OpenLightingProject/rp2040-dmxsun/src/tusb_lwip_glue.c

/* 
 * The MIT License (MIT)
 *
 * Based on tinyUSB example that is: Copyright (c) 2020 Peter Lawrence
 * Modified for Pico by Floris Bos
 *
 * influenced by lrndis https://github.com/fetisov/lrndis
 *
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
 */

#include "tusb_lwip_glue.h"
#include <pico/unique_id.h>

#include "log.h"

#include "boardconfig.h"
#include "dhcpdata.h"

extern uint8_t usbTraffic;

/* lwip context */
static struct netif netif_data;

/* shared between tud_network_recv_cb() and service_traffic() */
static struct pbuf *received_frame;

/* this is used by this code, ./class/net/net_driver.c, and usb_descriptors.c */
/* ideally speaking, this should be generated from the hardware's unique ID (if available) */
/* it is suggested that the first byte is 0x02 to indicate a link-local address */
uint8_t tud_network_mac_address[6] = {0x02,0x02,0x84,0x6A,0x96,0x00};

ip_addr_t ipaddr;
ip_addr_t netmask;
ip_addr_t gateway;

ip_addr_t hostIp;
ip_addr_t ownIp;

static err_t linkoutput_fn(struct netif *netif, struct pbuf *p)
{
    (void)netif;

    for (;;)
    {
        /* if TinyUSB isn't ready, we must signal back to lwip that there is nothing we can do */
        if (!tud_ready()) {
            return ERR_USE;
        }

        /* if the network driver can accept another packet, we make it happen */
        if (tud_network_can_xmit(p->tot_len))
        {
          tud_network_xmit(p, 0 /* unused for this example */);
          return ERR_OK;
        }
    
      /* transfer execution to TinyUSB in the hopes that it will finish transmitting the prior packet */
      tud_task();
     }
}

static err_t output_fn(struct netif *netif, struct pbuf *p, const ip_addr_t *addr)
{
    return etharp_output(netif, p, addr);
}

static void netif_status_callback(struct netif *nif)
{
  LOG("netif_status_callback: %c%c%d is %s\n", nif->name[0], nif->name[1], nif->num, netif_is_up(nif) ? "UP" : "DOWN");
}

static void netif_link_callback(struct netif *state_netif)
{
  if (netif_is_link_up(state_netif)) {
    LOG("netif_link_callback==UP\n");
  } else {
    LOG("netif_link_callback==DOWN\n");
  }
}

static err_t netif_init_cb(struct netif *netif)
{
    LOG("netif_init_cb");
    LWIP_ASSERT("netif != NULL", (netif != NULL));
    netif->mtu = CFG_TUD_NET_MTU;
    netif->flags = NETIF_FLAG_BROADCAST | NETIF_FLAG_ETHARP | NETIF_FLAG_LINK_UP | NETIF_FLAG_UP;
    netif->state = NULL;
    netif->name[0] = 'u'; // for "USB"
    netif->name[1] = '0';
    netif->linkoutput = linkoutput_fn;
    netif->output = output_fn;

    netif->hostname = getBoardHostnameString();

    return ERR_OK;
}

void init_tinyusb_netif(void)
{
    struct netif *netif = &netif_data;
    err_t igmp_result;
    
    /* Fixup MAC address based on flash serial */
    pico_unique_board_id_t id;
    pico_get_unique_board_id(&id);
    
    /* the lwip virtual MAC address must be different from the host's; to ensure this, we toggle the LSbit */
    netif->hwaddr_len = sizeof(tud_network_mac_address);
    memcpy(netif->hwaddr+1, (id.id)+1, sizeof(tud_network_mac_address)-1);
    netif->hwaddr[0] = 0x02;
    netif->hwaddr[5] ^= 0x01;

    ip4_addr_set_u32(&ipaddr, getOwnIp());
    ip4_addr_set_u32(&netmask, getOwnMask());
    ip4_addr_set_u32(&gateway, 0);
    
    netif = netif_add(netif, &ipaddr, &netmask, &gateway, NULL, netif_init_cb, ip_input);
    netif_set_status_callback(netif, netif_status_callback);
    netif_set_link_callback(netif, netif_link_callback);
    netif_set_default(netif);


    netif->flags |= NETIF_FLAG_IGMP;
    igmp_result = igmp_start( netif );
    LOG("IGMP START: %u", igmp_result);
}

void tud_network_init_cb(void)
{
    /* if the network is re-initializing and we have a leftover packet, we must do a cleanup */
    if (received_frame)
    {
      pbuf_free(received_frame);
      received_frame = NULL;
    }
}

bool tud_network_recv_cb(const uint8_t *src, uint16_t size)
{
    /* this shouldn't happen, but if we get another packet before 
    parsing the previous, we must signal our inability to accept it */
    if (received_frame) return false;

    usbTraffic = 1;
    
    if (size)
    {
        struct pbuf *p = pbuf_alloc(PBUF_RAW, size, PBUF_POOL);

        if (p)
        {
            /* pbuf_alloc() has already initialized struct; all we need to do is copy the data */
            memcpy(p->payload, src, size);
        
            /* store away the pointer for service_traffic() to later handle */
            received_frame = p;
        }
    }

    return true;
}

uint16_t tud_network_xmit_cb(uint8_t *dst, void *ref, uint16_t arg)
{
    struct pbuf *p = (struct pbuf *)ref;

    (void)arg; /* unused for this example */

    pbuf_copy_partial(p, dst, p->tot_len, 0);

    return p->tot_len;
}

void service_traffic(void)
{
    /* handle any packet received by tud_network_recv_cb() */
    if (received_frame)
    {
      ethernet_input(received_frame, &netif_data);
      pbuf_free(received_frame);
      received_frame = NULL;
      tud_network_recv_renew();
    }
    
    sys_check_timeouts();
}

// Should moved out of here, at least the "start DHCP server" part
void dhcpd_init()
{
    ip4_addr_set_u32(&hostIp, getHostIp());
    dhcp_entries_usb[0].addr = hostIp;
    dhcp_entries_usb[0].lease = 24 * 60 * 60;

    dhcp_config_usb->netif = &netif_data;

    while (dhserv_init(&dhcp_config) != ERR_OK);
}

void wait_for_netif_is_up()
{
    LOG("wait_for_netif_is_up: %u", netif_is_up(&netif_data));
    while (!netif_is_up(&netif_data));
}


/* lwip platform specific routines for Pico */
auto_init_mutex(lwip_mutex);
static int lwip_mutex_count = 0;
