OpenLightingProject/rp2040-dmxsun/src/lwipopts.h

/*
 * Copyright (c) 2001-2003 Swedish Institute of Computer Science.
 * All rights reserved. 
 * 
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
 * This file is part of the lwIP TCP/IP stack.
 * 
 * Author: Simon Goldschmidt
 *
 */
#ifndef __LWIPOPTS_H__
#define __LWIPOPTS_H__

/* Prevent having to link sys_arch.c (we don't test the API layers in unit tests) */
#define NO_SYS                          1
#define MEM_ALIGNMENT                   4
#define MEM_SIZE                        16384  // default: 1600
#define PBUF_POOL_SIZE                  24     // default: 16
#define MEMP_NUM_UDP_PCB                64
#define MEMP_NUM_TCP_PCB                16
#define MEMP_NUM_TCPIP_MSG_API          16
#define LWIP_RAW                        0
#define LWIP_NETCONN                    0
#define LWIP_SOCKET                     0
#define LWIP_DHCP                       1
#define LWIP_DNS                        1
#define LWIP_NETIF_HOSTNAME             1
#define LWIP_ICMP                       1
#define LWIP_UDP                        1
#define LWIP_TCP                        1
#define LWIP_SNMP                       0
#define LWIP_PPP                        0
#define LWIP_IPV6                       0
#define ETH_PAD_SIZE                    0
#define LWIP_IP_ACCEPT_UDP_PORT(p)      ((p) == PP_NTOHS(67))

#define LWIP_IGMP                       1
#define MEMP_NUM_IGMP_GROUP             32

#define TCP_MSS                         (1500 /*mtu*/ - 20 /*iphdr*/ - 20 /*tcphhr*/)
#define TCP_SND_BUF                     (2 * TCP_MSS)

#define ETHARP_SUPPORT_STATIC_ENTRIES   1

#define LWIP_NETIF_STATUS_CALLBACK      1
#define LWIP_NETIF_LINK_CALLBACK        1

#define LWIP_HTTPD_CGI                  1
#define LWIP_HTTPD_SSI                  1
#define LWIP_HTTPD_SSI_RAW              1
#define LWIP_HTTPD_MAX_TAG_NAME_LEN     64
#define LWIP_HTTPD_SSI_INCLUDE_TAG      0
#define LWIP_HTTPD_MAX_TAG_INSERT_LEN   2048

#define LWIP_HTTPD_SUPPORT_11_KEEPALIVE 1

#define HTTPD_USE_CUSTOM_FSDATA         1
#define HTTPD_FSDATA_FILE               "../../../../../src/fsdata.c"

#define LWIP_SINGLE_NETIF               0

// Defined in https://github.com/raspberrypi/pico-examples/blob/master/pico_w/lwipopts_examples_common.h
#define LWIP_NETIF_TX_SINGLE_PBUF   1
#define MEM_LIBC_MALLOC             1

#endif /* __LWIPOPTS_H__ */
