OpenLightingProject/rp2040-dmxsun/src/dmxbuffer.h

#ifndef DMXBUFFER_H
#define DMXBUFFER_H

#include <cstdint>
#include <stdio.h>

#ifndef DMXBUFFER_COUNT
#define DMXBUFFER_COUNT 24
#endif // DMXBUFFER_COUNT

#ifdef __cplusplus

// Class that stores and manages ALL internal "main" DMX buffers
class DmxBuffer {
  public:
    static uint8_t buffer[DMXBUFFER_COUNT][512];
    static uint8_t allZeroes[512]; // Array of 512 zero-bytes to be used with memcmp for performance
    void init();
    void zero(uint8_t bufferId);
    bool getBuffer(uint8_t bufferId, uint8_t* dest, uint16_t destLength); // alias "copyTo"
    bool setBuffer(uint8_t bufferId, uint8_t* source, uint16_t sourceLength); // alias "copyFrom"
    bool getChannel(uint8_t bufferId, uint16_t channel, uint8_t* value);
    bool setChannel(uint8_t bufferId, uint16_t channel, uint8_t value);

    bool isAllZero(uint8_t bufferId);

  private:
    void triggerPatchings(uint8_t bufferId, bool allZero = false);
    bool allZeroBuffers[DMXBUFFER_COUNT];
};

#endif // __cplusplus

// Helper methods which are called from C code
#ifdef __cplusplus
extern "C" {
#endif

// None yet :)

#ifdef __cplusplus
}
#endif

#endif // DMXBUFFER_H
