OpenLightingProject/rp2040-dmxsun/src/version.h

#define VERSION "1.0.0"

// Version number reported in the USB device descriptor
// Since no one cares about "bug fixes" there, we report first and second
// digit of VERSION here, which means we are limited to 255 per digit :(
#define VERSION_BCD 0x0100
